tobychui/DezKVM/designs/diff.png

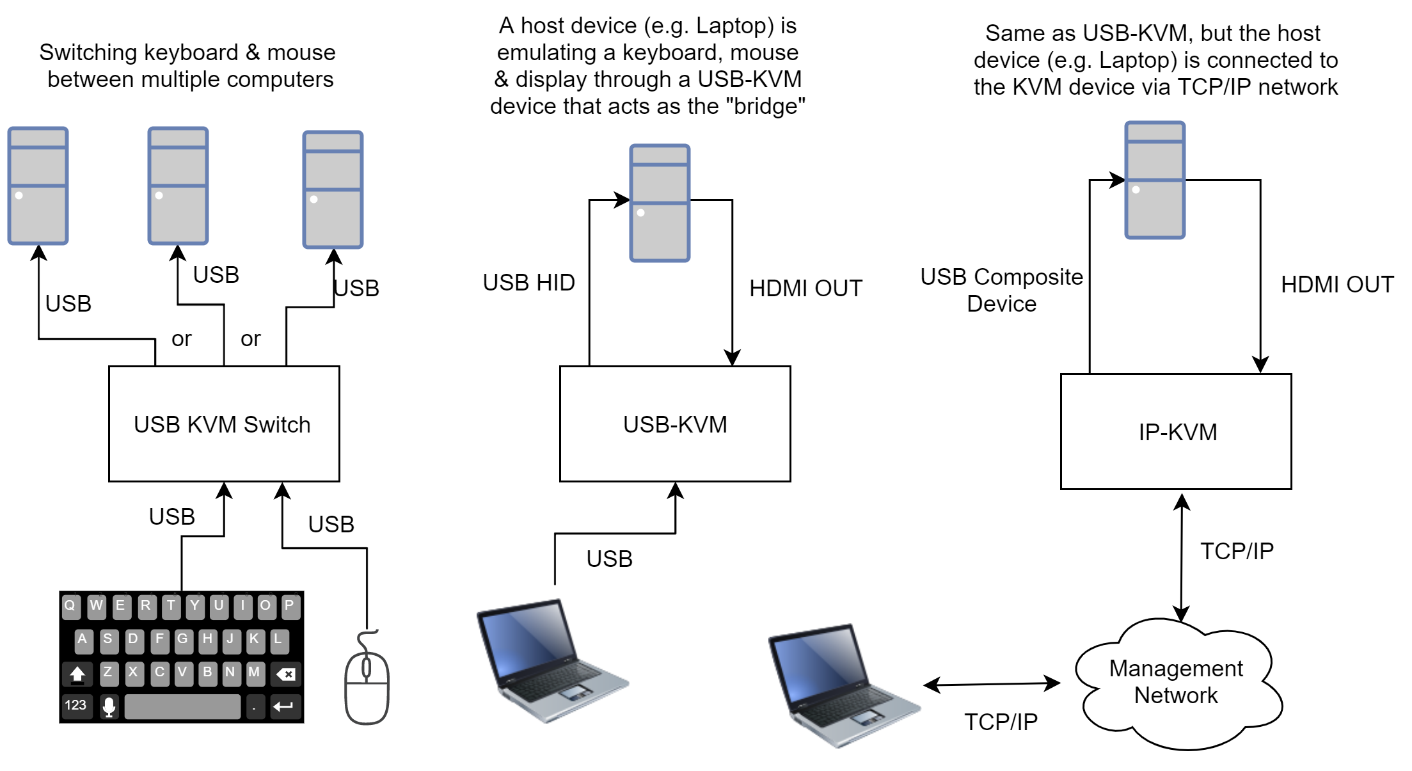
designs/diff.png
