tobychui/DezKVM/hardware/DezKVM Production/3d_models/PFF_single_port/Screenshot 2026-03-02 at 20-43-00 0.96寸OLED显示屏模块0.91 1.3 1.54寸12864液晶屏4_6_7针IIC_SPI-tmall.com天猫.png

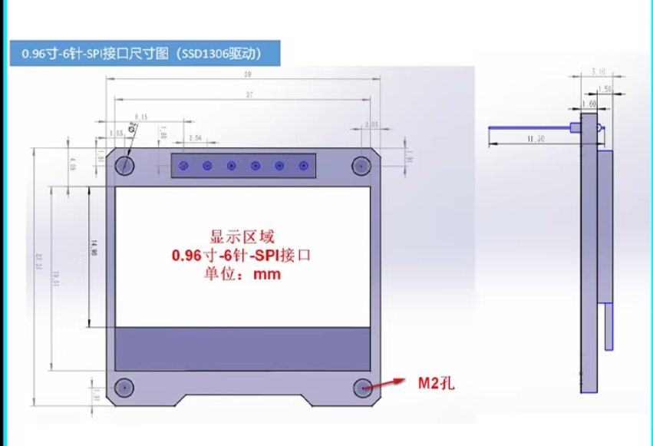
hardware/DezKVM Production/3d_models/PFF_single_port/Screenshot 2026-03-02 at 20-43-00 0.96寸OLED显示屏模块0.91 1.3 1.54寸12864液晶屏4_6_7针IIC_SPI-tmall.com天猫.png
