tobychui/DezKVM/hardware/DezKVM Production/3d_models/PFF_single_port/Screenshot 2026-03-14 at 12-59-36 0.96寸OLED显示屏模块SPI 1.3 0.91 液晶12864彩屏幕4针6 ssd1306-tmall.com天猫.png

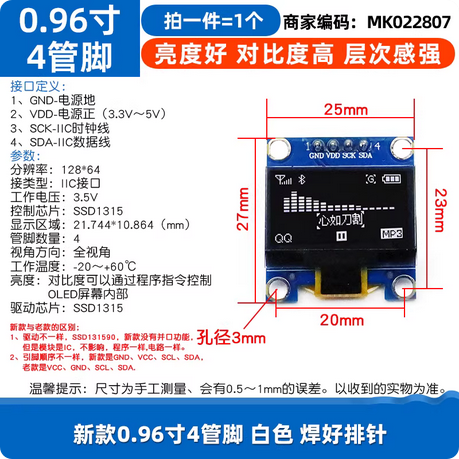
hardware/DezKVM Production/3d_models/PFF_single_port/Screenshot 2026-03-14 at 12-59-36 0.96寸OLED显示屏模块SPI 1.3 0.91 液晶12864彩屏幕4针6 ssd1306-tmall.com天猫.png
