tobychui/DezKVM/hardware/DezKVM PoC/3d_models/capture_holder_bottom_filled.stl

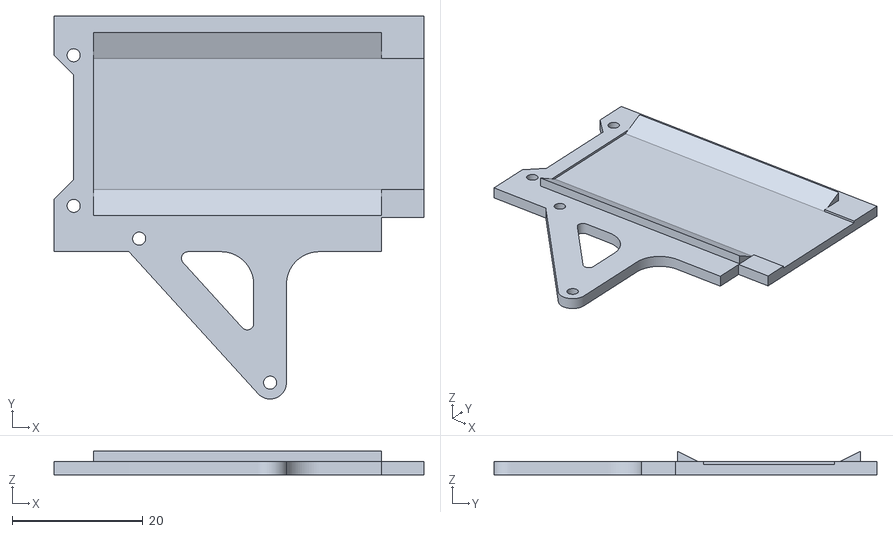
[picture p40: CAD file, 2026-04-04]
hardware/DezKVM PoC/3d_models/capture_holder_bottom_filled.stl
56.5 x 58.5 x 3.60
