tobychui/DezKVM/hardware/DezKVM Production/3d_models/PFF_single_port/front-panel.stl

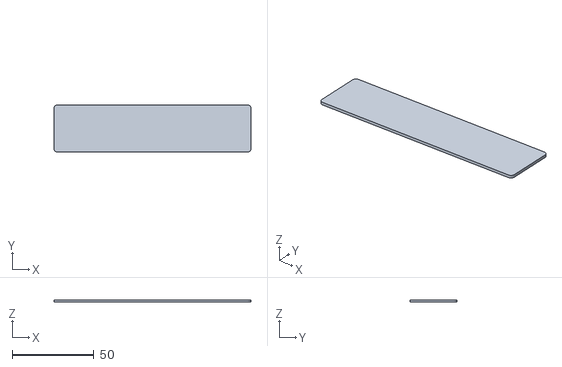
[picture p41: CAD file, 2026-04-04]
hardware/DezKVM Production/3d_models/PFF_single_port/front-panel.stl
120.2 x 28.7 x 1.50
