tobychui/DezKVM/hardware/DezKVM Production/3d_models/PFF_v1_base/bridge_structure_A.stl

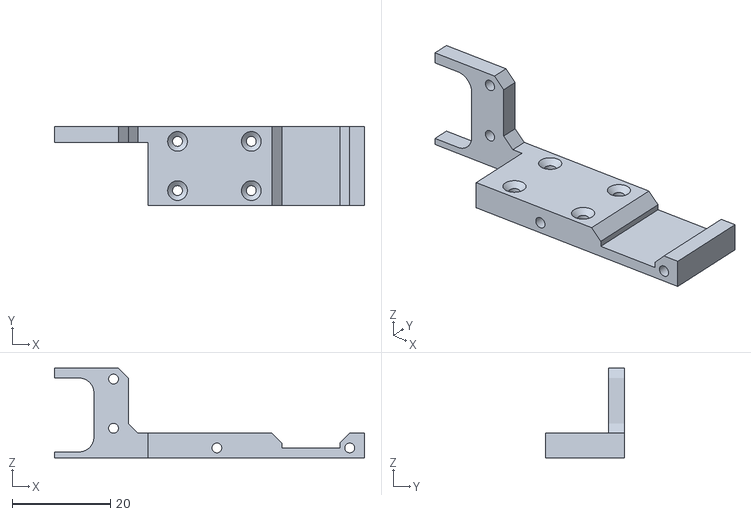
[picture p42: CAD file, 2026-04-04]
hardware/DezKVM Production/3d_models/PFF_v1_base/bridge_structure_A.stl
63.0 x 16.0 x 18.2
