tobychui/DezKVM/hardware/USB_KVM_Switch/3D models/bottom_no-hdmi.stl

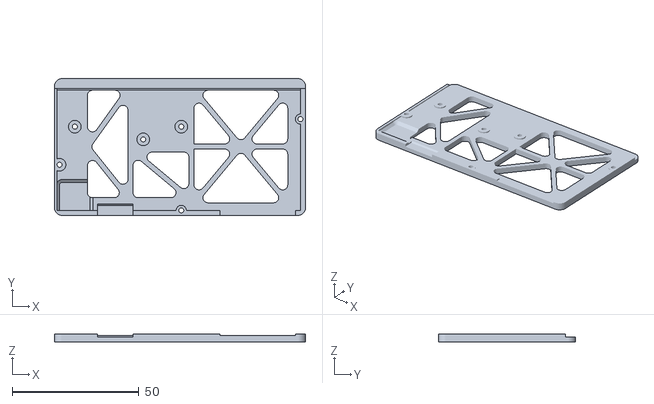
[picture p43: CAD file, 2026-05-04]
hardware/USB_KVM_Switch/3D models/bottom_no-hdmi.stl
99.0 x 54.0 x 3.10
