tobychui/DezKVM/hardware/DezKVM PoC/3d_models/capture_holder_top.stl

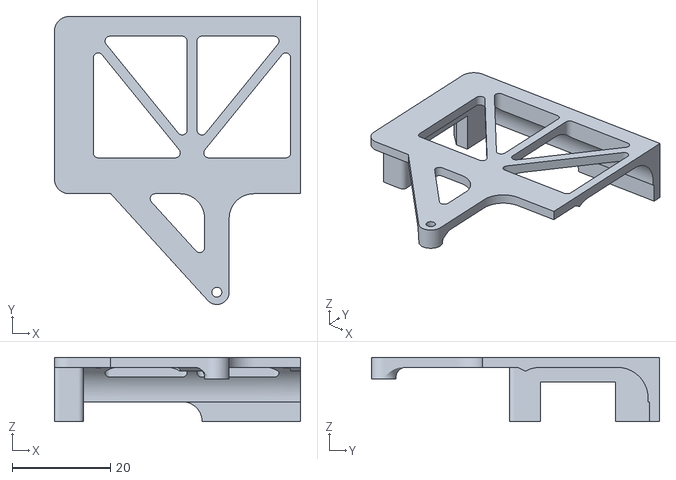
[picture p44: CAD file, 2026-04-04]
hardware/DezKVM PoC/3d_models/capture_holder_top.stl
50.0 x 58.5 x 13.0
