tobychui/DezKVM/hardware/DezKVM Production/3d_models/PFF_single_port/structural.stl

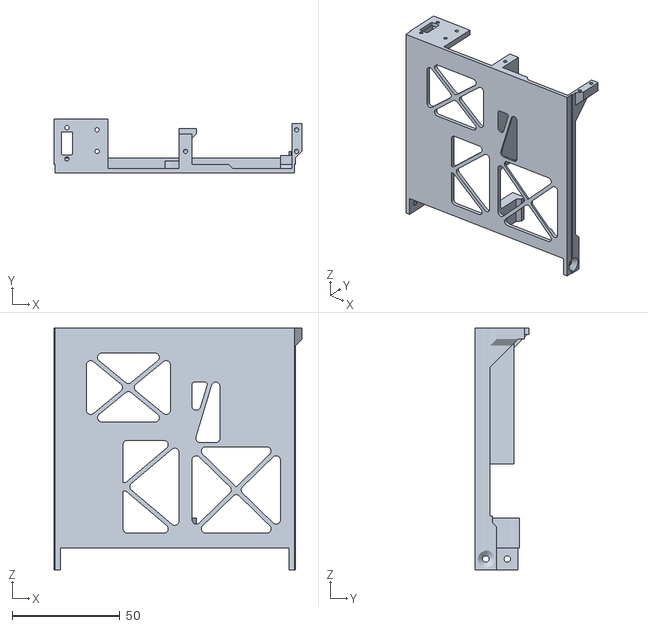
[picture p45: CAD file, 2026-04-04]
hardware/DezKVM Production/3d_models/PFF_single_port/structural.stl
115.0 x 25.0 x 112.0
