tobychui/DezKVM/hardware/DezKVM Production/3d_models/PFF_v1_base/hdmi_base_plate.stl

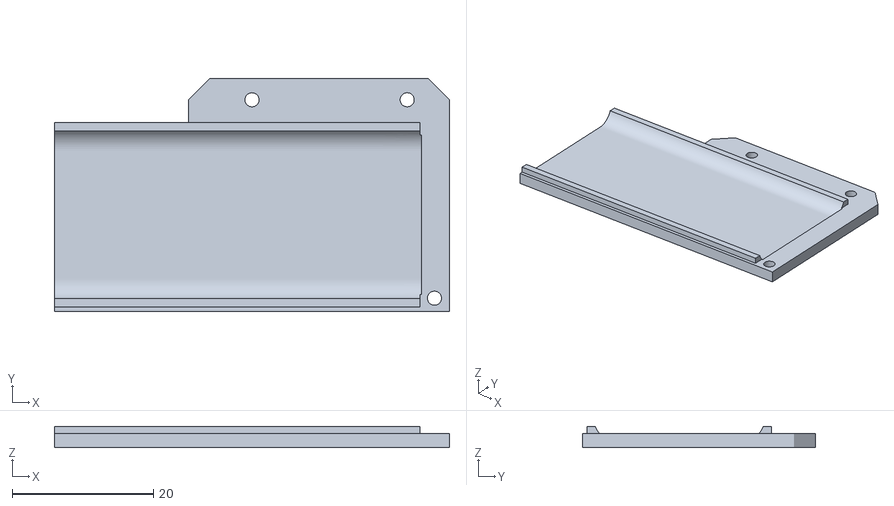
[picture p46: CAD file, 2026-04-04]
hardware/DezKVM Production/3d_models/PFF_v1_base/hdmi_base_plate.stl
56.0 x 33.0 x 3.00
