tobychui/DezKVM/hardware/USB_KVM_Switch/3D models/bottom.stl

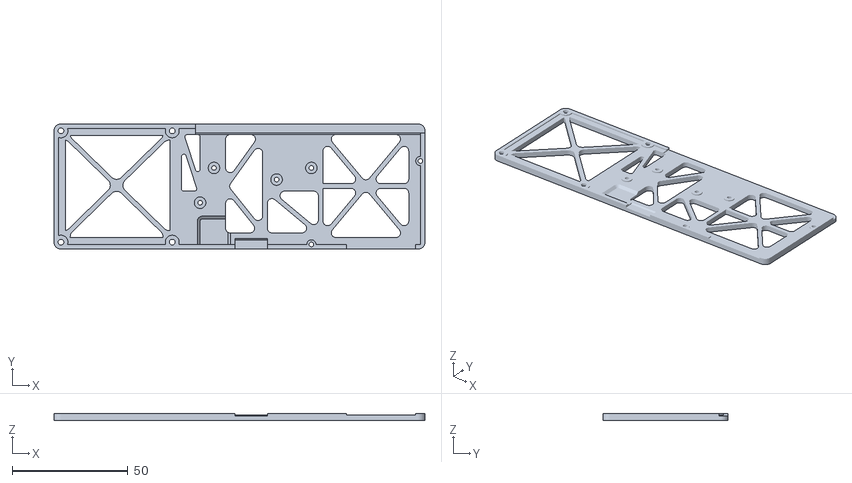
[picture p47: CAD file, 2026-05-04]
hardware/USB_KVM_Switch/3D models/bottom.stl
160.0 x 54.0 x 3.10
