tobychui/DezKVM/hardware/DezKVM Production/3d_models/PFF_single_port/case_dummy.stl

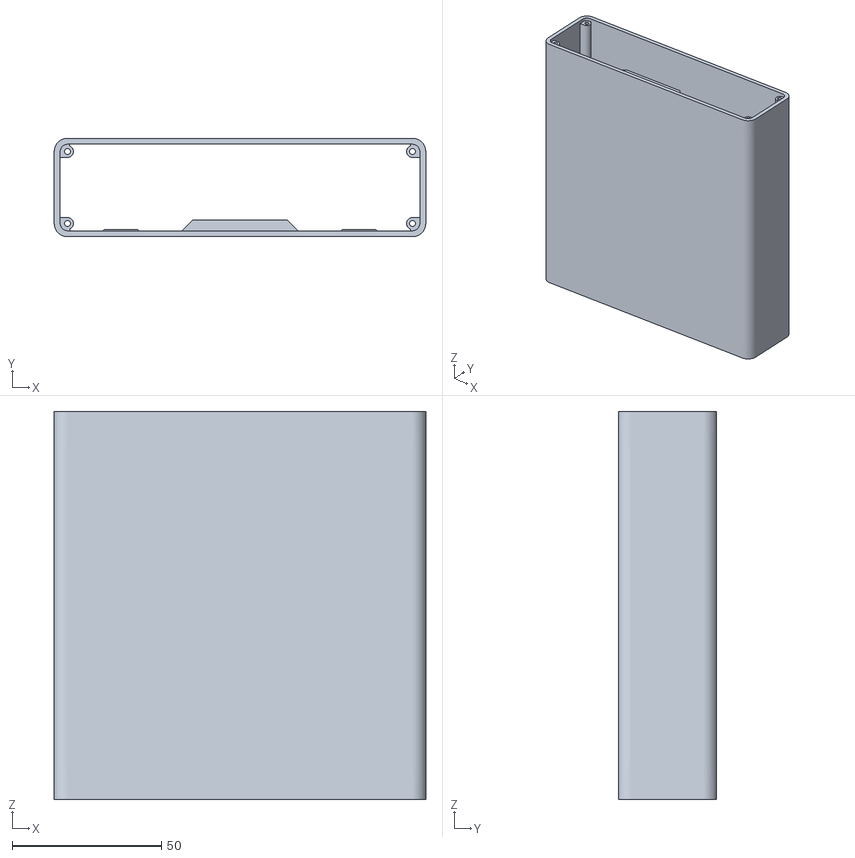
[picture p48: CAD file, 2026-04-04]
hardware/DezKVM Production/3d_models/PFF_single_port/case_dummy.stl
124.5 x 33.0 x 130.0
