tobychui/DezKVM/hardware/USB_KVM_Switch/3D models/test_plate.stl

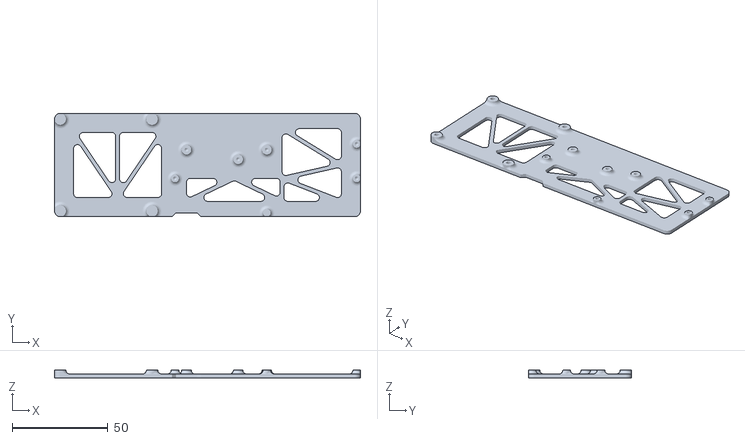
[picture p49: CAD file, 2026-05-04]
hardware/USB_KVM_Switch/3D models/test_plate.stl
160.0 x 54.0 x 4.00
